sivakov512/esp32h2-switch/main/driver.h

#pragma once

#include <esp_err.h>
#include <soc/gpio_num.h>

class Driver {
public:
  explicit Driver();

  esp_err_t Init();

  esp_err_t SetRelayState(bool val);

  esp_err_t SetLedState(bool val);

private:
  gpio_num_t relay_gpio_;
  gpio_num_t led_gpio_;
};
